mg-mods/iut-lyon1-but-geii-sae-6/HF/SImulation FM/schémas final.asc

A1: xor
C1: cap; 10n
C2: cap; 10p
C3: cap; 10n
C4: cap; 470p
C5: cap; 1n
C6: cap; 1n
C7: cap; 10p
C8: cap; 1µ
C9: cap; 10n
C10: cap; 1µ
C11: cap; 1n
R1: res; 150
R2: res; 1200
R3: res; 560
R4: res; 1k
R5: res; 10k
R6: res; 5600
R7: res; 1200
R8: res; 1k
R9: res; 150
R10: res; 1k
R11: res; 47K
U1: MAX74821
V1: signal; PULSE(0 5 0 1p 1p {Duty13} {T13} {Ncycle13})
V2: signal; PULSE(0 3.3 0 0.0000001 0.0000001 {Duty} {T} {Ncycle})
V3: voltage; 5
Named nets: vcomod, microout, 0, filtre_100k, oscilateur, antenne, mel2, filtre_pb_100k, Demodul, Vco, filtre_13M, Microin
Bvco vcomod 0 V = 2.5 + 2.5*sgn(sin(2*pi*idt( {Fp}*(1 + 0.05*((V(microout)-1.5))) )))
bvmel1 antenne 0 V = V(filtre_100k)*V(filtre_13M)
bvmel2 mel2  0 V = V(antenne)*V(oscilateur)
===> VCO====>
Bvcodemod Vco 0 V = 2.5 + 2.5*sgn(sin(2*pi*idt( {Fp}*(1 + 0.1*(V(Demodul) - 0.5)))))
.param R=1000
;op
.tran 0 {Tsim} 10n
.param F=9600 T=1/{F} F13=13560000 T13=1/{F13} Duty13=T13/2 Fp=100000 Tp=1/Fp Duty2=Tp/2 Duty=T/2 Tsim=0.002 Ncycle=Tsim/T Ncycle13=Tsim/T13 Ncycle2=Tsim/Tp
