mg-mods/iut-lyon1-but-geii-sae-6/HF/SImulation FM/Draft1.asc

A1: xor
C1: cap; 100n
C2: cap; 10p
C3: cap; 10n
C4: cap; 470p
C5: cap; 0.000000002
C6: cap; 1n
R1: res; 150
R2: res; 1,2k
R3: res; 560
R4: res; 1k
R5: res; 10000
R6: res; 5600
V1: signal; PULSE(0 1 1p 1p {Duty2} {Tp} {Ncycle2})
V2: signal; PULSE(0 1 0 0.0000001 0.0000001 {Duty} {T} {Ncycle})
Named nets: vcomod, microout, 0, filtre_100k, oscilateur, filtre_13M, mel, antenne, mel2, filtre_pb_100k, Demodul, Vco, Microin
Bvco vcomod 0 V = 2.5 + 2.5*sgn(sin(2*pi*idt( {Fp}*(1 + 0.05*(V(microout) - 0.5)) )))
bvmel1 mel 0 V = V(filtre_100k)*V(filtre_13M)
bvmel2 mel2  0 V = V(mel)*V(oscilateur)
===> VCO====>
Bvcodemod Vco 0 V = 2.5 + 2.5*sgn(sin(2*pi*idt( {Fp}*(1 + 0.1*(V(Demodul) - 0.5)))))
.param R=1000
;op
.tran 0 {Tsim} 10n
.param F=1000 T=1/{F} Fp=13000000 Tp=1/Fp Duty2=Tp/2 Duty=T/2 Tsim=0.1 Ncycle=Tsim/T Ncycle2=Tsim/Tp
;ac dec 100 10000 1000000
